Ifousoft/Chronometre_Arc/Chronometre/A2.c

/* GIMP RGB C-Source image dump (A2.c) */

typedef struct  {
  unsigned int   width;
  unsigned int   height;
  unsigned int   bytes_per_pixel; /* 2:RGB16, 3:RGB, 4:RGBA */
  unsigned char  pixel_data[64*32*3 + 1];
} gimp_bitmap_a2;

static const gimp_bitmap_a2 gimp_a2 = {
  64, 32, 3,
  "\000\000\000\000\000\000\000\000\000\000j\061\000\231H\001\233G\010\254@\017\277\067\026\322)\031\333\037"
  "\020\301\066\002\236F\000\231H\000\231H\000\231H\000\231H\000\231H\000\231H\000\231H\000\231"
  "H\000\231H\000\231H\000\231H\000\231H\000\231H\000\231H\000\231H\000}:\000c,\000\231H\331\350"
  "\336\375\376\375C\244d\000\231H\040\235R\335\352\340\232\305\246\000\231H\000\231"
  "H\000\231H\000\231H\000\231H\000\231H\000\231H\000\231H\007\254@\030\331\"\021\303\064\000\232"
  "H\000\225G\000A\037\000\000\000\000\000\000\000\000\000\000\000\000\000\000\000\000\000\000\000\000\000\000\000\000\000\000\000\000\000"
  "\000\000\000\000\000\000\000\000\000\000\000\000\000\000\000\000\000\000\000\000\213A\000\231H\027\326%\025\320+\020\300"
  "\066\007\254@\000\231H\000\231H\000\231H\000\231H\000\231H\000\231H\000\231H\000\231H\000\231"
  "H\000\231H\000\231H\000\231H\000\231H\000\231H\000\231H\000\231H\000\231H\000\231H\000])\000\201"
  "<\000\231H\255\316\266\377\377\377\237\307\252\000\231Hi\255{\377\377\377\304"
  "\333\312\000\231H\000\231H\000\231H\000\231H\000\231H\000\231H\000\231H\000\231H\000\231H\001"
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
  "H\014\267;\031\334\037\016\273\071\000\231H\000\231H\000w\067\000\017\007\000\000\000\000\000\000\000\000"
  "\000\000\000\000\000\000\000\000\000\000\000\000\000\000\000\000\000\000\000\000\000\000\000\000\000\000\000\000\000\000\000",
};
