Ifousoft/Chronometre_Arc/Chronometre/Abbaye.c

/* GIMP RGB C-Source image dump (Abbaye.c) */

// this structre can hold up to a 32x32 pixel RGB bitmap
typedef struct  {
  unsigned int   width;
  unsigned int   height;
  unsigned int   bytes_per_pixel; /* 2:RGB16, 3:RGB, 4:RGBA */
  unsigned char  pixel_data[50*64*3 + 1];
} gimp_bitmap;

static const gimp_bitmap abbaye = {
  50, 64, 3,
  "\377\377\377\377\377\377\377\377\377\377\377\377\377\377\377\377\377\377"
  "\377\377\377\377\377\377\376\376\375\376\376\375\375\376\376\375\376\375"
  "\375\376\375\374\377\375\367\375\372\363\374\367\361\374\366\325\357\341"
  "\277\344\320\265\335\305\257\331\277\247\325\271\243\322\266\242\321\265"
  "\242\321\265\242\321\265\242\321\266\243\321\265\244\325\270\252\330\276"
  "\262\335\306\276\343\317\351\371\360\364\374\367\364\374\371\366\374\371"
  "\370\375\373\374\376\375\375\376\376\375\376\375\376\376\376\376\376\376"
  "\376\376\376\377\377\377\377\377\377\377\377\377\377\377\377\377\377\377"
  "\377\377\377\377\377\377\377\377\377\377\377\377\377\377\377\377\377\377"
  "\377\377\377\377\377\377\377\377\377\377\376\376\376\376\374\374\376\374"
  "\371\376\374\337\363\350\306\344\322\274\342\314q\274\220Q\256yA\246l-\240"
  "`\032\235W\022\233R\014\231O\007\230K\004\227H\004\227G\005\227F\004\227G\004\226G\004\227"
  "H\006\230J\013\231N\023\232T\033\234X\066\244f@\245lL\254vc\267\211\177\304\236"
  "\267\337\307\315\351\331\341\363\351\372\376\375\374\376\376\376\376\376"
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
  "\377\377\377\377\377\377\377\377\377\377\377\377\377\377\377\377\377\377"
  "\377\377\377\377\377\377\377\377\377\377\377\377\377\377\377\377\377\377"
  "\377\377\377\377\377\377\377\377\377\377\377\377\377\377\377\377\377\377"
  "\377\377\377\377\377\377\377\377\377\377\377\377\377\377\377\377\377\377"
  "\377\377\377\377\377\377\377\377\377\377\377\377\377\377\377\377\377\377"
  "\377\377\377\377\377\377\377\377\377\377\377\377\377\377\377\377\377\377"
  "\377\377\377\377\377\377\377\377\377\377\377\377\377\377\377\377\377\376"
  "\376\375\364\365\363\357\360\355\336\336\335\363\364\364\372\371\371\375"
  "\377\376\377\377\377\377\377\377\377\377\377\377\377\377\377\377\377\377"
  "\377\377\377\377\377\377\377\377\377\377\377\377\377\377\377\377\377\377"
  "\377\377\377\377\377\377\377\377\377\377\377\377\377\377\377\377\377\377"
  "\377\377\377\377\377\377\377\377\377\377\377",
};
