Ifousoft/Chronometre_Arc/Chronometre/Logo.ifou.c

/* GIMP RGB C-Source image dump (Logo.ifou.c) */

typedef struct  {
  unsigned int   width;
  unsigned int   height;
  unsigned int   bytes_per_pixel; /* 2:RGB16, 3:RGB, 4:RGBA */
  unsigned char  pixel_data[64*29*3 + 1];
} gimp_bitmap_logo_ifou;

static const gimp_bitmap_logo_ifou logo_ifou = {
  64, 29, 3,
  "\000\000\000\000\000\000\000\000\000\000\000\000\000\000\000\000\000\000\000\000\000\000\000\000\000\000\000\000\000\000\000\000\000\000\000\000"
  "\000\000\000\000\000\000\000\000\000\000\000\000\000\000\000\000\000\036\000\001P\000\001P\000\001P\000\001P\000\001P\000\001P\000\001P"
  "\000\001P\000\001P\000\001H\000\000'\000\000\000\000\000\000\000\000\000\000\000\000\000\000\000\000\000\000\000\000\000\000\000\000\000\000"
  "\000\000\000\000\000\000\000\000\000\000\000\000\000\000\000\000\000\000\000\000\000\000\000\000\000\000\000\000\000\000\000\000\000\000\000\000"
  "\000\000\000\000\000\000\000\000\000\000\000\000\000\000\000\000\000\000\000\000\000\000\000\000\000\000\000\000\000\000\000\000\000\000\000\000"
  "\000\000\000\000\000\000\000\000\000\000\000\000\000\000\000\000\000\000\000\000\000\000\000\000\000\000\000\000\000\000\000\000\000\000\000\000"
  "\000\000\000\000\000\000\000\000\000\000\000\000\000\000\000\000\000\000\000\000\000\000\000\001^\000\003\377\000\003\377\000\003\377"
  "\000\003\377\000\003\377\000\003\377\000\003\377\000\003\377\000\003\377\000\003\377\000\003\376\000\002\214"
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
  "\000\000\000\000\000\000\000\000\000\000\000\000\000\000\000\000\000\000\000\000\000\000\000\000\000\000\000\000\000\000\000\000\000\000\000\000"
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
};
