Ifousoft/Chronometre_Arc/Chronometre/A1.c

/* GIMP RGB C-Source image dump (A1.2.c) */

// this structre can hold up to a 32x32 pixel RGB bitmap
typedef struct  {
  unsigned int   width;
  unsigned int   height;
  unsigned int   bytes_per_pixel; /* 2:RGB16, 3:RGB, 4:RGBA */
  unsigned char  pixel_data[64*8*3 + 1];
} gimp_bitmap_a1;

static const gimp_bitmap_a1 gimp_a1 = {
  64, 8, 3,
  "\000\000\000\000\000\000\000\000\000\000\000\000\000\000\000\000\001\000\000\015\006\000\061\027\000f\060\000\206?\000\206?\000"
  "\207>\021\261*\022\264'\000\206?\000\206?\000\206?\000\206?\000\206?\000\206?\000\206?\000"
  "\206?\000\206?\000\206?\000\206?\000\206?\000\206?\000\206?\000D\035\016z<\331\334\333\310"
  "\322\314\000\206>\000\206?\000\206?\000\206?\000\206?\000\206?\000\206?\000\206?\000\206?\000"
  "\206?\010\233\066\026\277\035\022\262(\002\214=\000\206?\000\205>\000D\040\000\001\000\000\000\000"
  "\000\000\000\000\000\000\000\000\000\000\000\000\000\000\000\000\000\000\000\000\000\000\000\000\000\000\000\000\000\000\000\000\000\000\000\000"
  "\000\000\000\000\000\000\000\000\000\000\000\000\000\000\000\000\000\000\000\000\000\000\000\000\000\000\000\000\000\000\000(\023\000\203"
  ">\000\231H\000\232H\025\320+\016\275\070\000\231H\000\231H\000\231H\000\231H\000\231H\000\231"
  "H\000\231H\000\231H\000\231H\000\231H\000\231H\000\231H\000\231H\000q\064T\207e\377\377\377"
  "\313\337\321\000\231H\000\231H\000\231H\000\231H\000\231H\000\231H\000\231H\000\232H\012\262"
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
  "\000\000\000\000\000\000\000\000\000\000\000\000\000\000\015\006\000\222E\000\231H\000\231H\000\231H\000\231H\000\231"
  "H\000\231H\000\231H\000\231H\000\231H\000\231H\000\231H\000\231H\000\231H\000\231H\000\231H\000"
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
};
