Ifousoft/Chronometre_Arc/Chronometre/A3.c

/* GIMP RGB C-Source image dump (A3.c) */

typedef struct  {
  unsigned int   width;
  unsigned int   height;
  unsigned int   bytes_per_pixel; /* 2:RGB16, 3:RGB, 4:RGBA */
  unsigned char  pixel_data[64*9*3 + 1];
} gimp_bitmap_a3;

static const gimp_bitmap_a3 gimp_a3 = {
  64, 9, 3,
  "\000\000\000\000\000\000\000\000\000\000\000\000\000\000\000\000\000\000\000\000\000\000\000\000\000\000\000\000\000\000\000\000\000\000\000\000"
  "\000\000\000\000\000\000\000\000\000\000\000\000\000\005\002\000\033\015\000)\023\000\071\033\000A\036\000E!\000L$\000O%\000"
  "N%\000H\"\000B\037\000=\034\000,\024\000\035\016\000\004\002\000\000\000\000\000\000\000\000\000\000\000\000\000\000\000\000\000"
  "\000\000\000\000\000\000\000\000\000\000\000\000\000\000\000\000\000\000\000\000\000\000\000\000\000\000\000\000\000\000\000\000\000\000\000\000"
  "\000\000\000\000\000\000\000\000\000\000\000\000\000\000\000\000\000\000\000\000\000\000\000\000\000\000\000\000\000\000\000\000\000\000\000\000"
  "\000\000\000\000\000\000\000\000\000\000\000\000\000\000\000\000\000\000\000\000\000\000\000\000\000\000\000\000\000\000\000\000\000\000\000\000"
  "\000\000\000\000\000\000\000\000\000\000\000\000\000\000\017\007\000|:\000\217C\000\231H\000\231H\000\231H\000\231H"
  "\000\231H\000\231H\000\231H\000\231H\000\231H\000\231H\000\231H\000\231H\000\231H\000\231H\000"
  "\230H\000\214B\000s\066\000T(\000\064\031\000\013\005\000\000\000\000\000\000\000\000\000\000\000\000\000\000\000\000\000\000"
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
  "\325'\014\270;\000\231H\000\231H\000\231H\000\231H\000\231H\000\231H\000\231H\000\231H\000\231"
  "H\000\231H\000\231H\000\231H\000\231H\000v\066o\220z\375\376\376\233\305\246\000\231H"
  "\000\231H\000\231H\000\231H\000\231H\000\231H\000\231H\003\242E\021\303\064\031\334\036\022"
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
};
